kikaizaru-art/robot-dev/chassis/neck.step

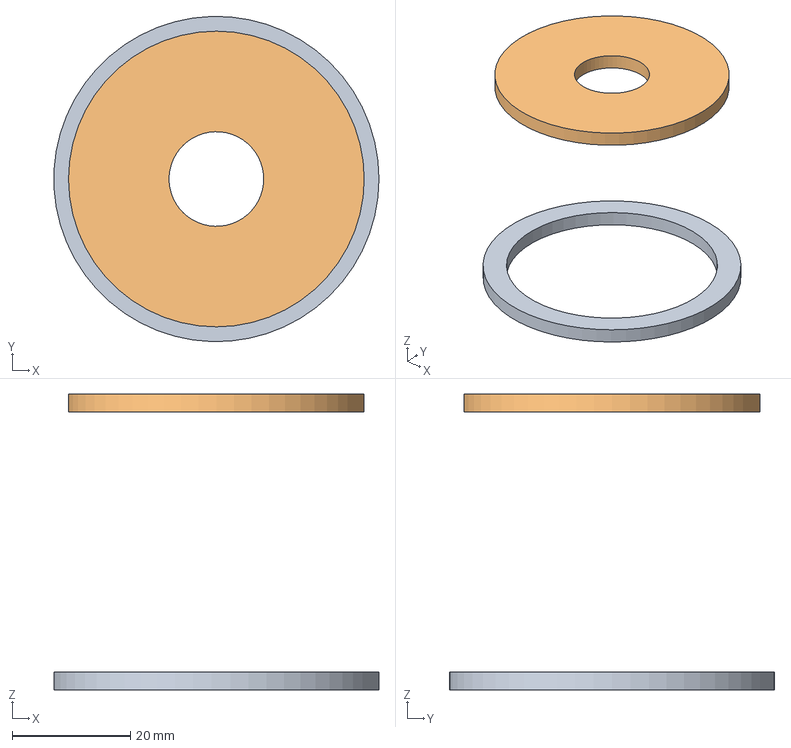
[picture p21: CAD file, 2026-03-30]
chassis/neck.step
55.0 x 55.0 x 50.0 mm
