kikaizaru-art/robot-dev/chassis/body.step

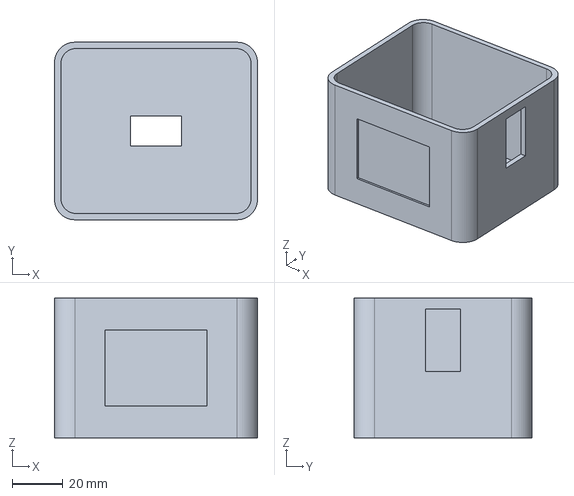
[picture p22: CAD file, 2026-03-30]
chassis/body.step
80.0 x 70.0 x 55.0 mm
