kikaizaru-art/robot-dev/chassis/head.step

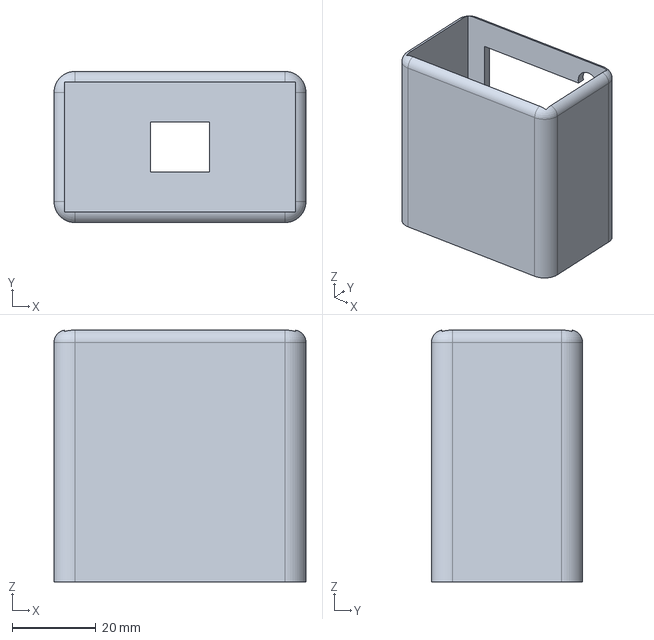
[picture p23: CAD file, 2026-03-30]
chassis/head.step
60.0 x 36.0 x 60.0 mm
